juanmcasillas/ArduSpinner/img/arduino.jpg

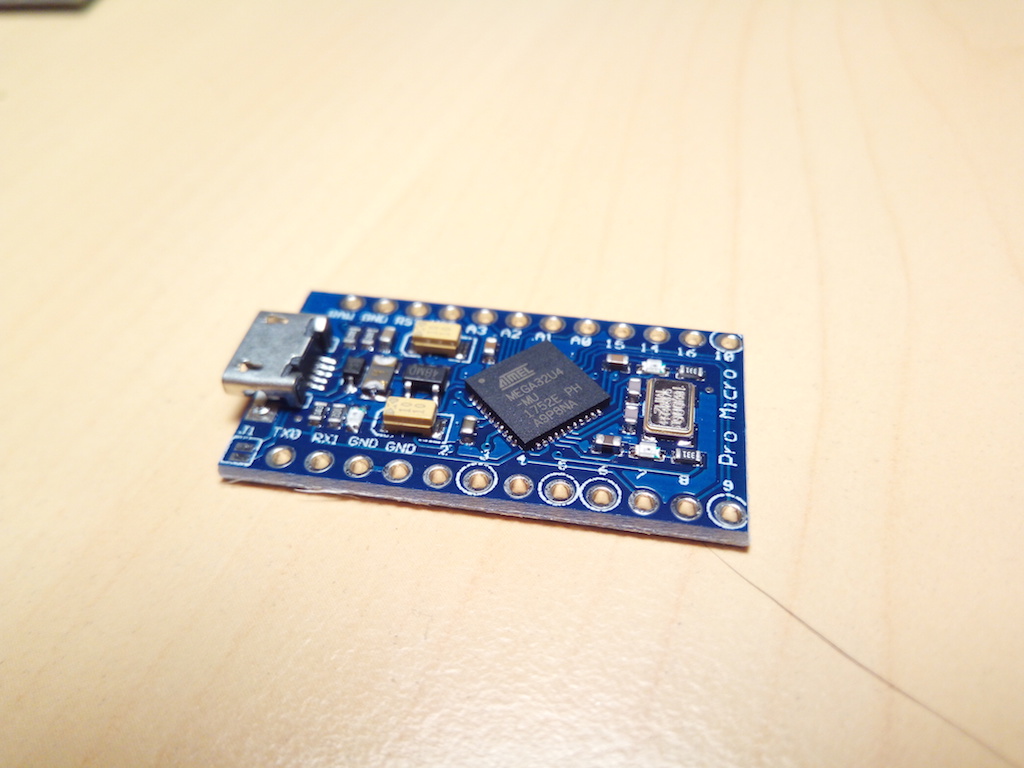
img/arduino.jpg
