juanmcasillas/ArduSpinner/wiring.sch

## EAGLE design wiring.sch (2020-07-27)

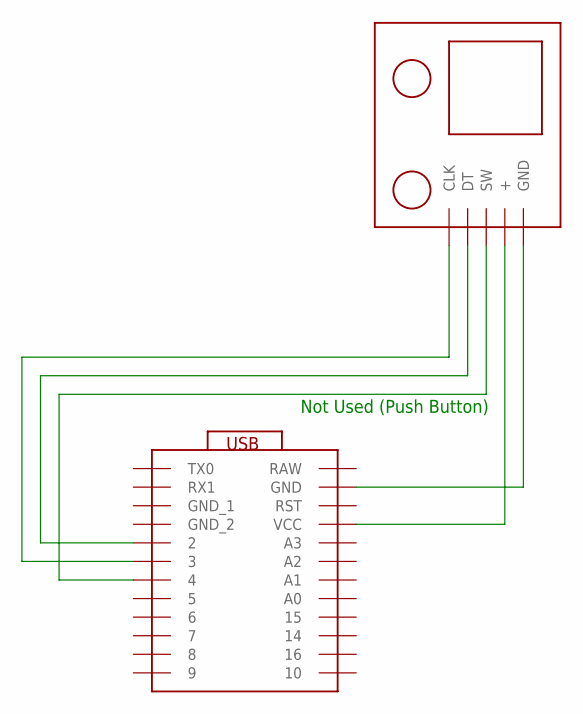
[picture p24: schematic wiring.sch]

Parts:
U$1: ARDUINOMICROCLONE
U$2: ENCODER

Connections:
unnamed: U$1.GND, U$2.GND
unnamed: U$1.VCC, U$2.+
unnamed: U$1.2, U$2.DT
unnamed: U$1.3, U$2.CLK
unnamed: U$1.4, U$2.SW

Notes on the sheet:
Not Used (Push Button)
