juanmcasillas/ArduSpinner/dev/test1/test1.ino

// https://www.luisllamas.es/arduino-encoder-rotativo/

const int channelPinA = 2;
const int channelPinB = 3;
 
const int timeThreshold = 5;
long timeCounter = 0;
 
const int maxSteps = 255;
volatile int ISRCounter = 0;
int counter = 0;
 
bool IsCW = true;
 
void setup()
{
   pinMode(channelPinA, INPUT_PULLUP);
   pinMode(channelPinB, INPUT_PULLUP);
   Serial.begin(115200);
   attachInterrupt(digitalPinToInterrupt(channelPinA), doEncodeA, CHANGE);
   attachInterrupt(digitalPinToInterrupt(channelPinB), doEncodeB, CHANGE);
}
 
void loop()
{
   if (counter != ISRCounter)
   {
      counter = ISRCounter;
      Serial.println(counter);
   }
   delay(1);
}
 
void doEncodeA()
{
   if (millis() > timeCounter + timeThreshold)
   {
      if (digitalRead(channelPinA) == digitalRead(channelPinB))
      {
         IsCW = true;
         if (ISRCounter + 1 <= maxSteps) ISRCounter++;
      }
      else
      {
         IsCW = false;
         if (ISRCounter - 1 > 0) ISRCounter--;
      }
      timeCounter = millis();
   }
}
 
void doEncodeB()
{
   if (millis() > timeCounter + timeThreshold)
   {
      if (digitalRead(channelPinA) != digitalRead(channelPinB))
      {
         IsCW = true;
         if (ISRCounter + 1 <= maxSteps) ISRCounter++;
      }
      else
      {
         IsCW = false;
         if (ISRCounter - 1 > 0) ISRCounter--;
      }
      timeCounter = millis();
   }
}
